jp112sdl/SplitFlap/Images/IMG_0931.jpeg

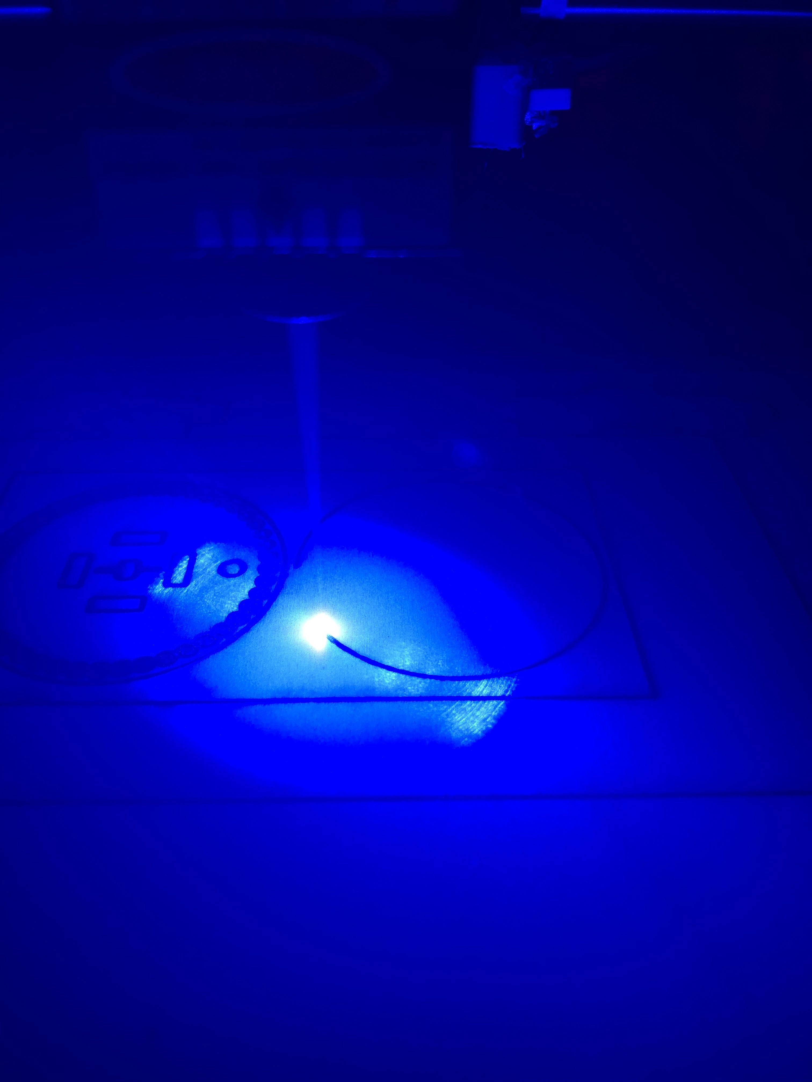
Images/IMG_0931.jpeg
