jp112sdl/SplitFlap/Images/IMG_0937.jpg

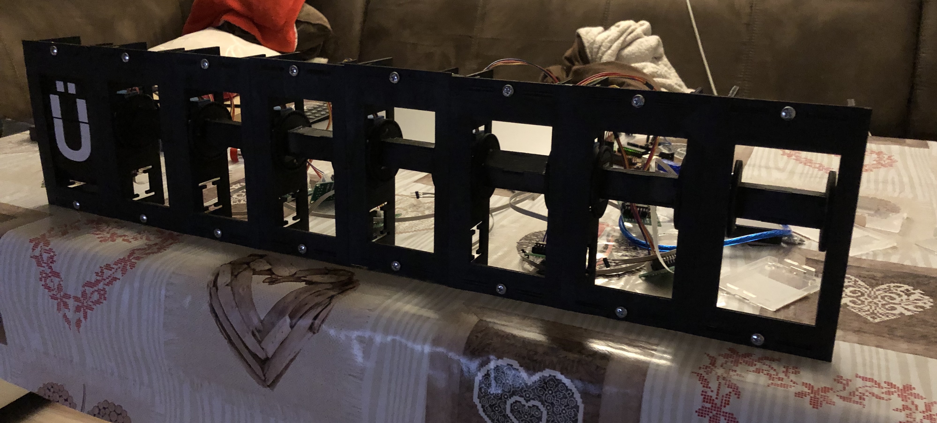
Images/IMG_0937.jpg
