jp112sdl/SplitFlap/Images/IMG_0946.jpeg

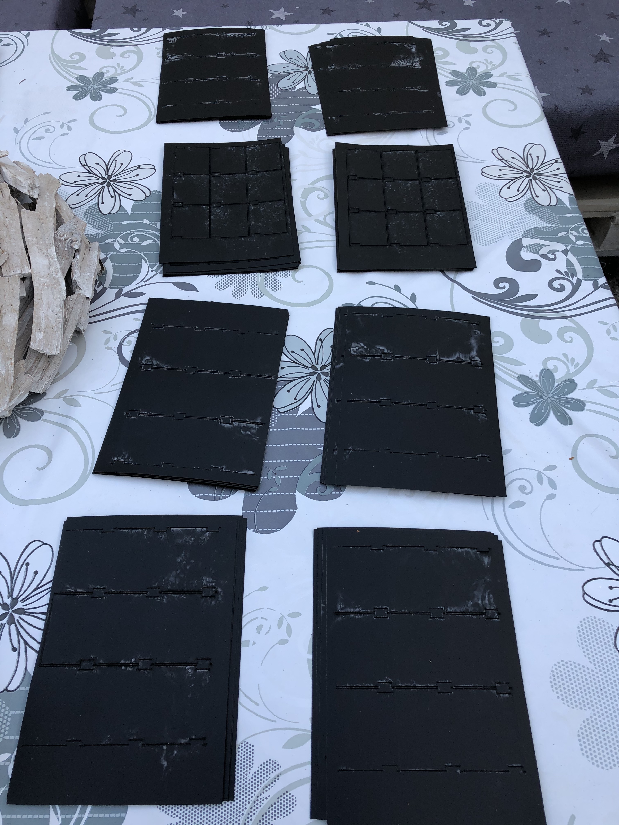
Images/IMG_0946.jpeg
