jp112sdl/SplitFlap/Images/IMG_0947.jpeg

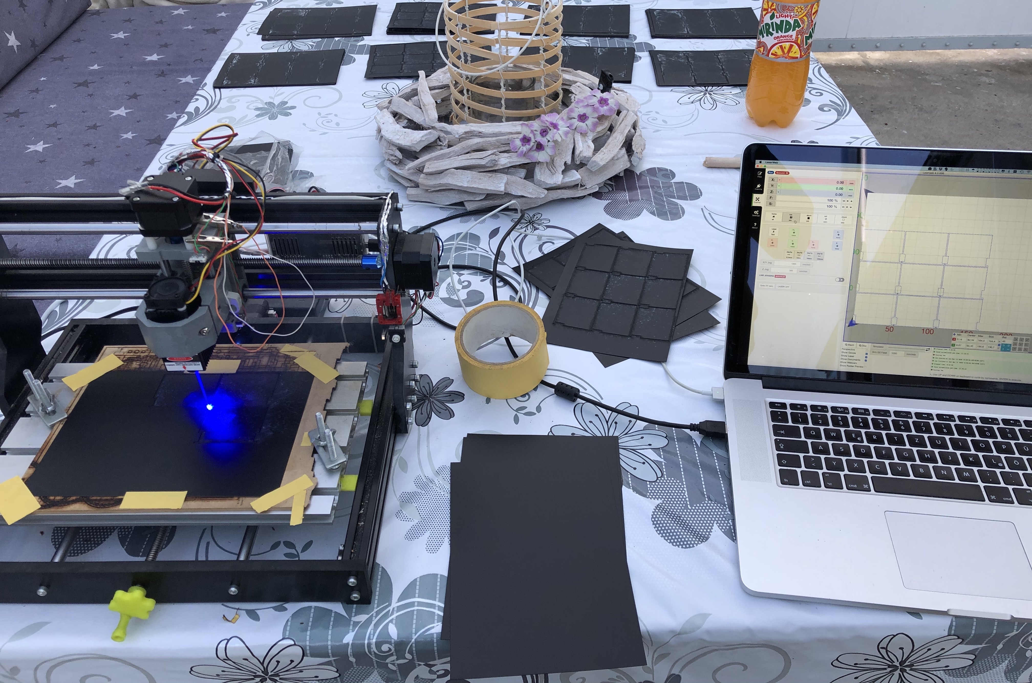
Images/IMG_0947.jpeg
