jp112sdl/SplitFlap/Images/IMG_0949.jpeg

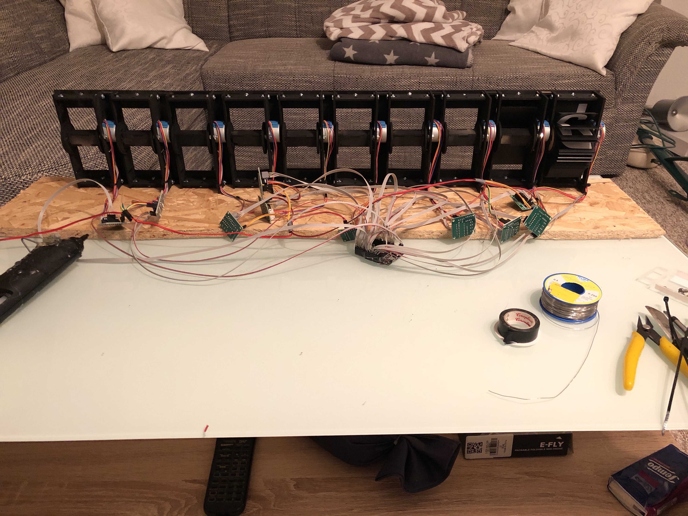
Images/IMG_0949.jpeg
