jp112sdl/SplitFlap/Images/IMG_0950.jpeg

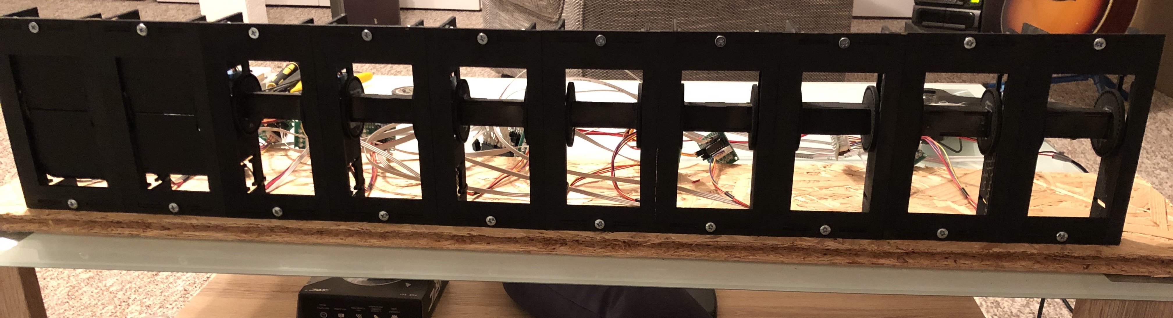
Images/IMG_0950.jpeg
