jp112sdl/SplitFlap/Images/IMG_0952.jpeg

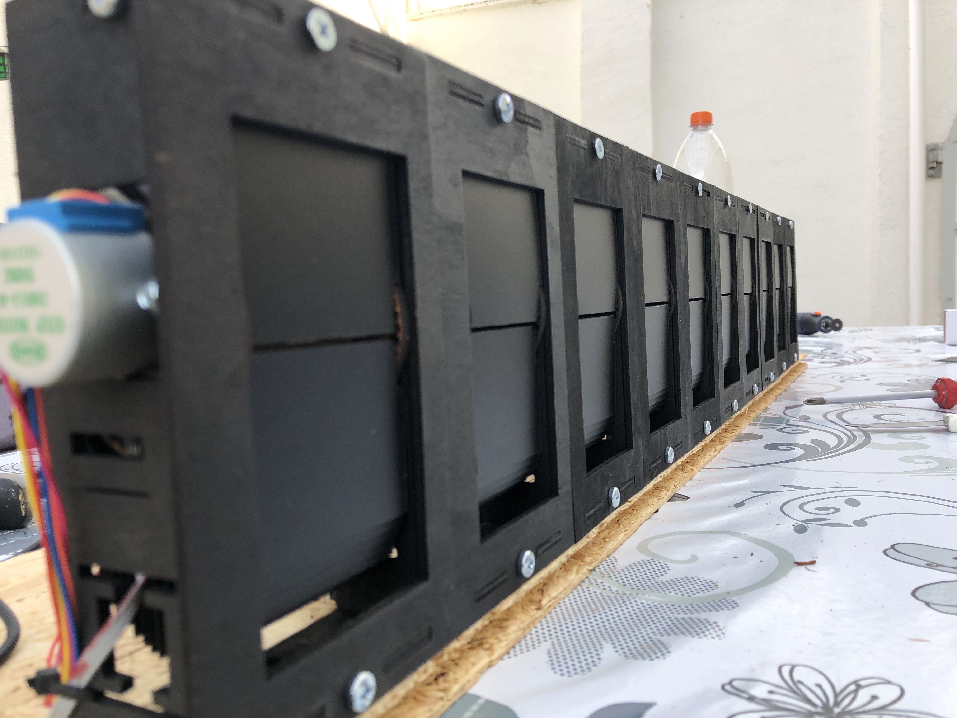
Images/IMG_0952.jpeg
