jp112sdl/SplitFlap/Images/IMG_0957.jpeg

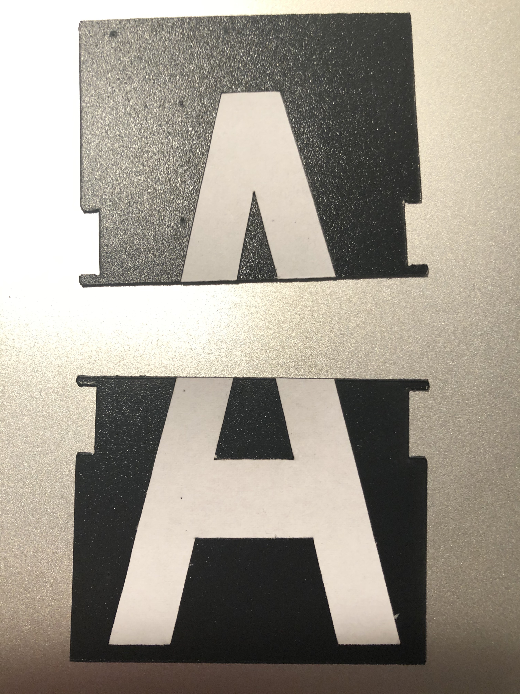
Images/IMG_0957.jpeg
