jp112sdl/SplitFlap/Images/IMG_0958.jpeg

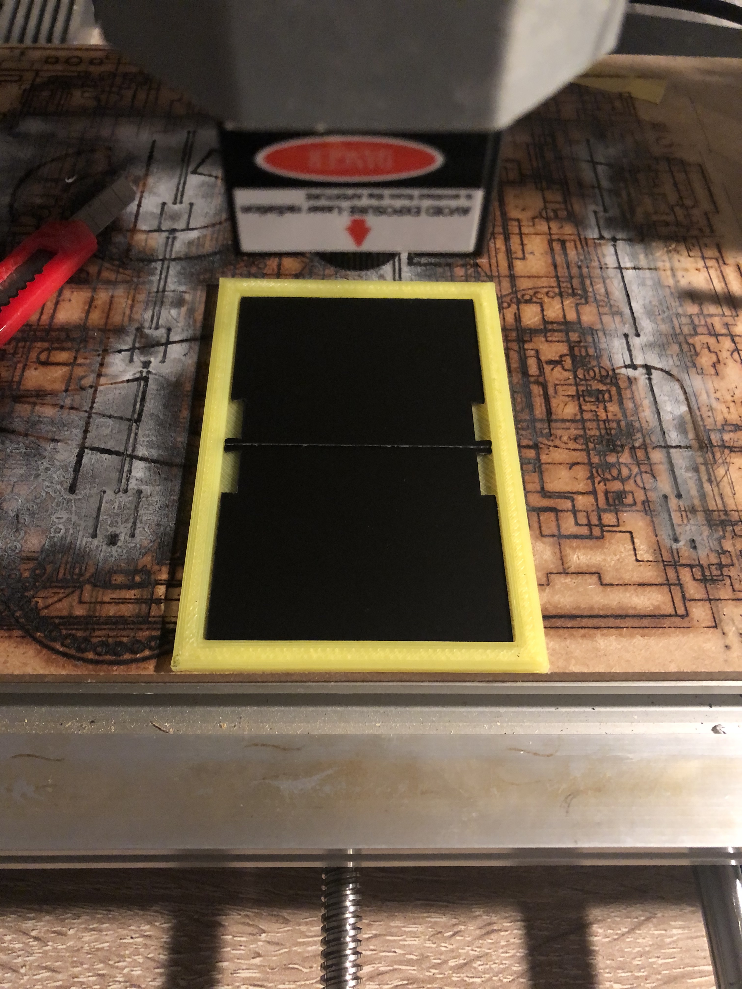
Images/IMG_0958.jpeg
