jp112sdl/SplitFlap/Images/IMG_0959.jpeg

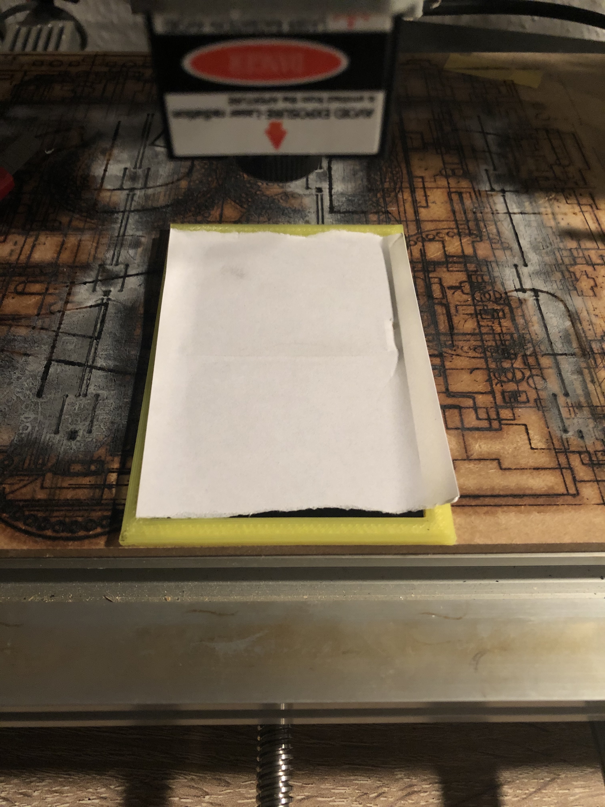
Images/IMG_0959.jpeg
