jp112sdl/SplitFlap/Images/IMG_0960.jpeg

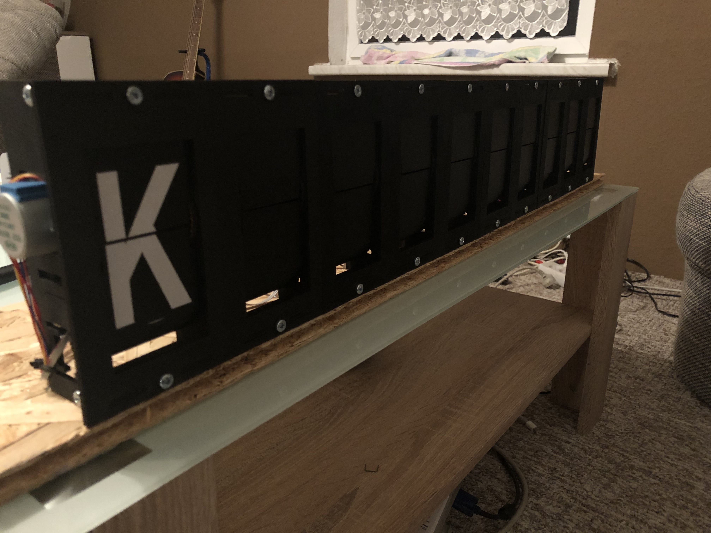
Images/IMG_0960.jpeg
