jp112sdl/SplitFlap/Images/IMG_0961.jpeg

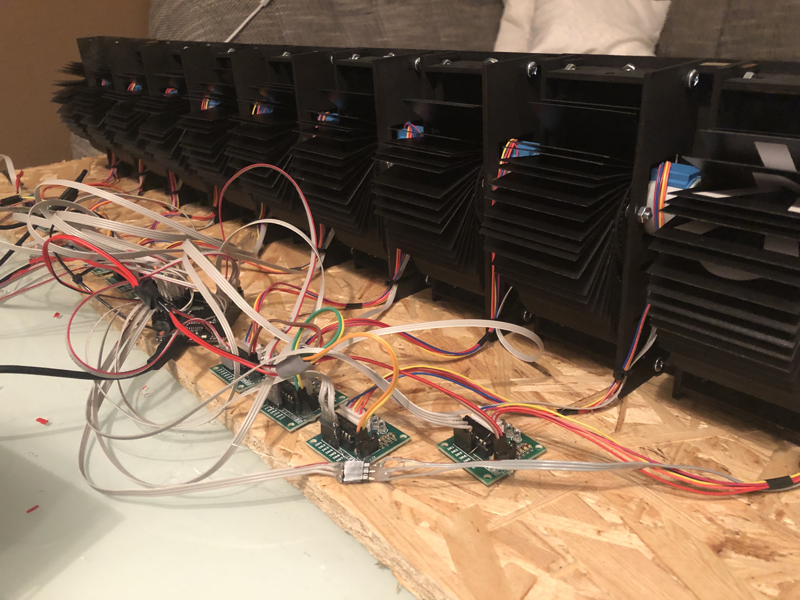
Images/IMG_0961.jpeg
