jp112sdl/SplitFlap/Images/IMG_0974.jpeg

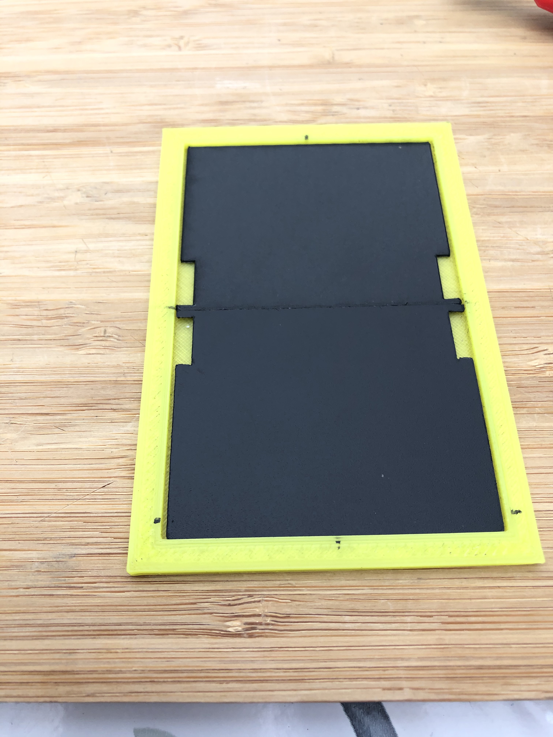
Images/IMG_0974.jpeg
