jp112sdl/SplitFlap/Images/IMG_0975.jpeg

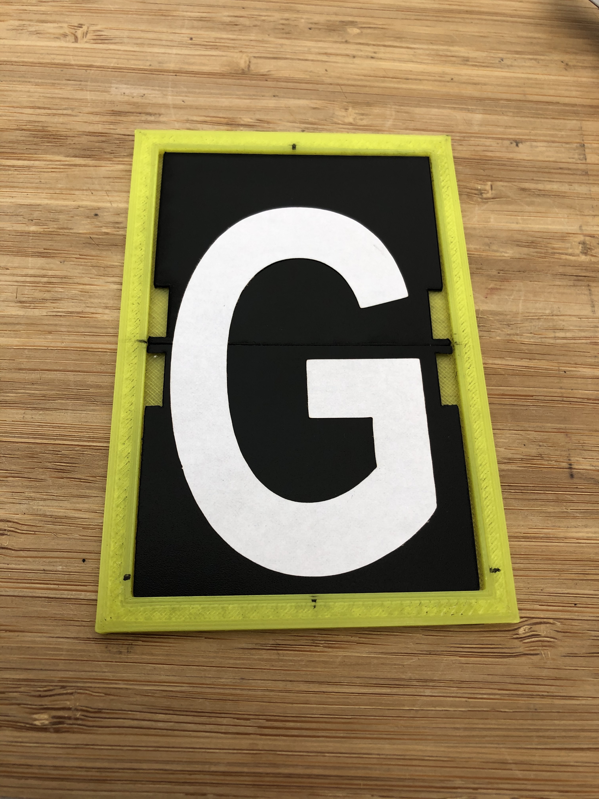
Images/IMG_0975.jpeg
