jp112sdl/SplitFlap/Images/IMG_0976.jpeg

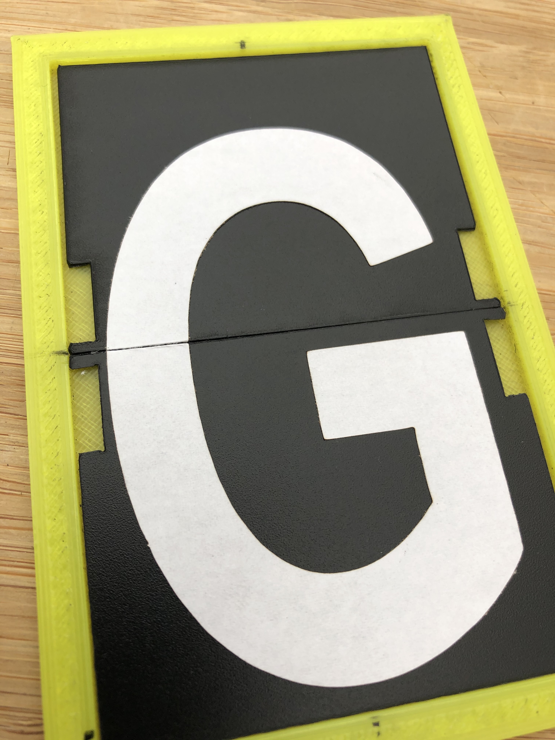
Images/IMG_0976.jpeg
