jp112sdl/SplitFlap/Images/IMG_0977.jpeg

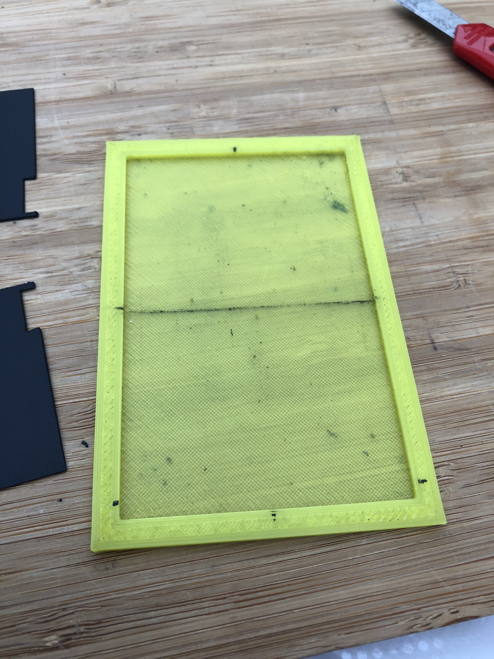
Images/IMG_0977.jpeg
