jp112sdl/SplitFlap/Images/IMG_0981.jpeg

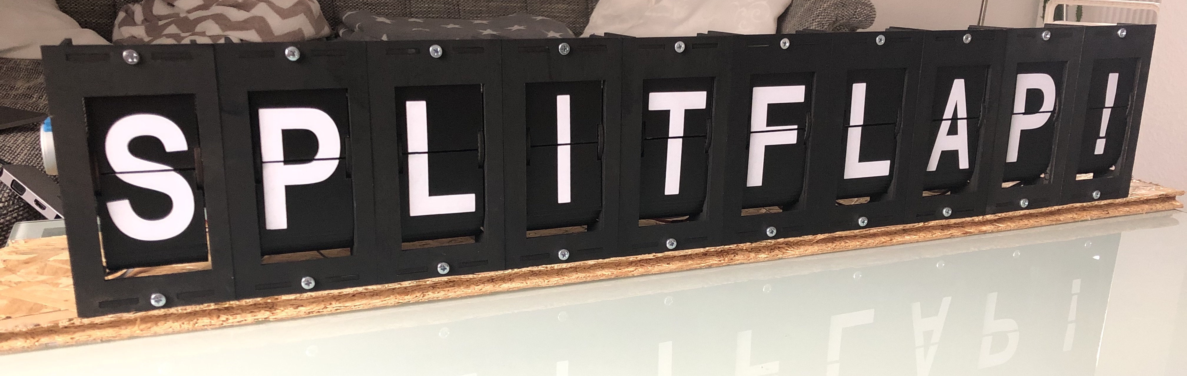
Images/IMG_0981.jpeg
