jp112sdl/SplitFlap/Images/IMG_0982.jpeg

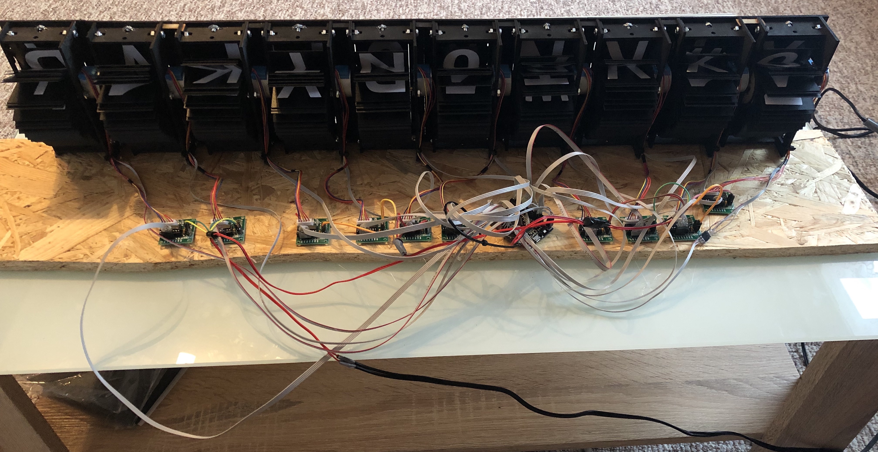
Images/IMG_0982.jpeg
