jp112sdl/SplitFlap/Images/IMG_1015.jpeg

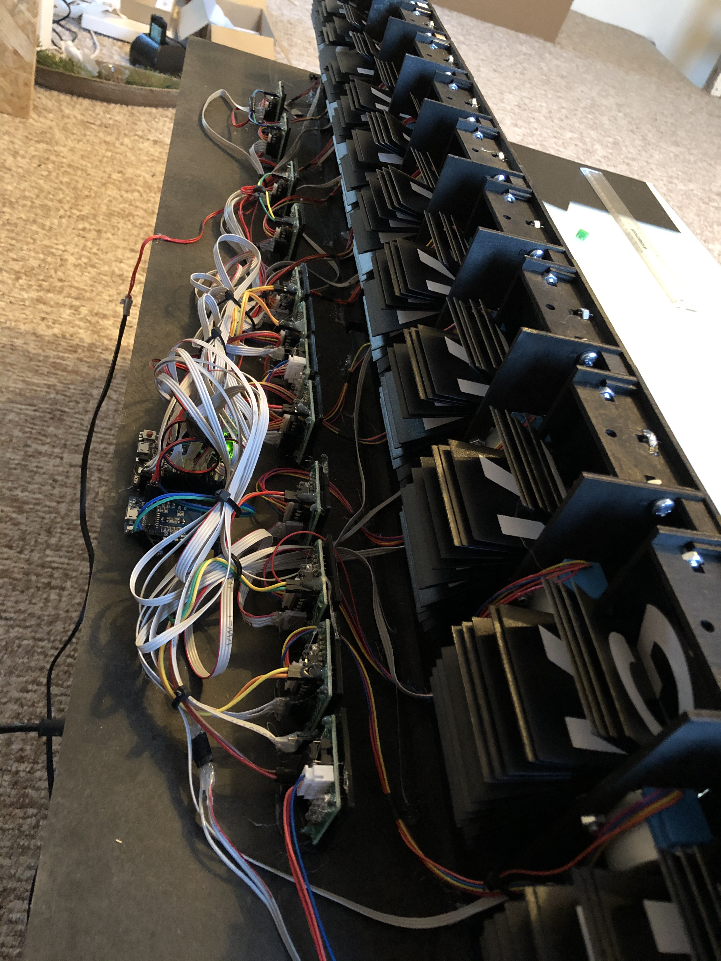
Images/IMG_1015.jpeg
