jp112sdl/SplitFlap/Images/IMG_1018.jpeg

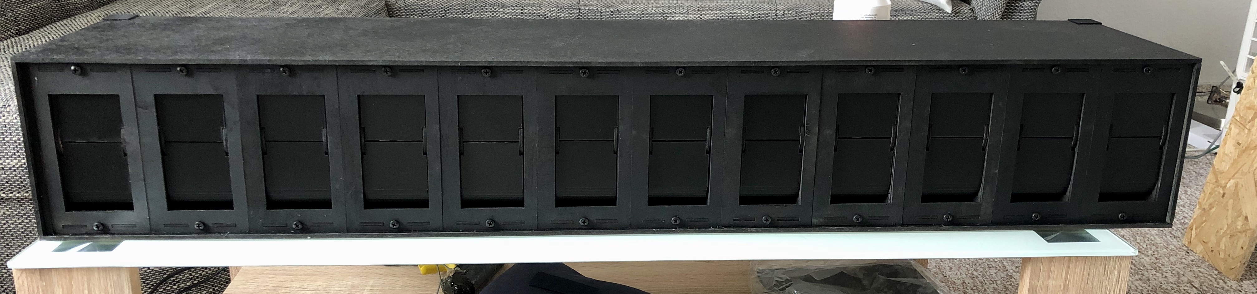
Images/IMG_1018.jpeg
