jp112sdl/SplitFlap/Images/IMG_1021.jpeg

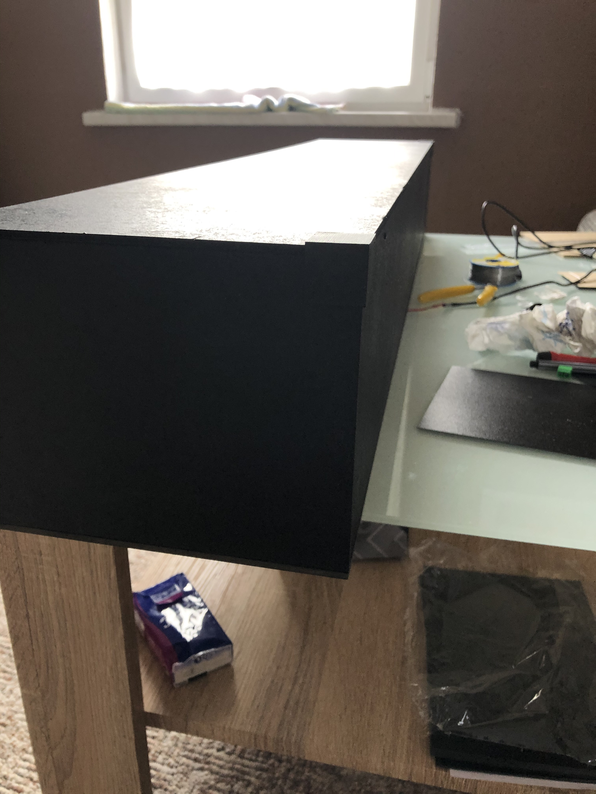
Images/IMG_1021.jpeg
