jp112sdl/SplitFlap/Images/IMG_1025.jpeg

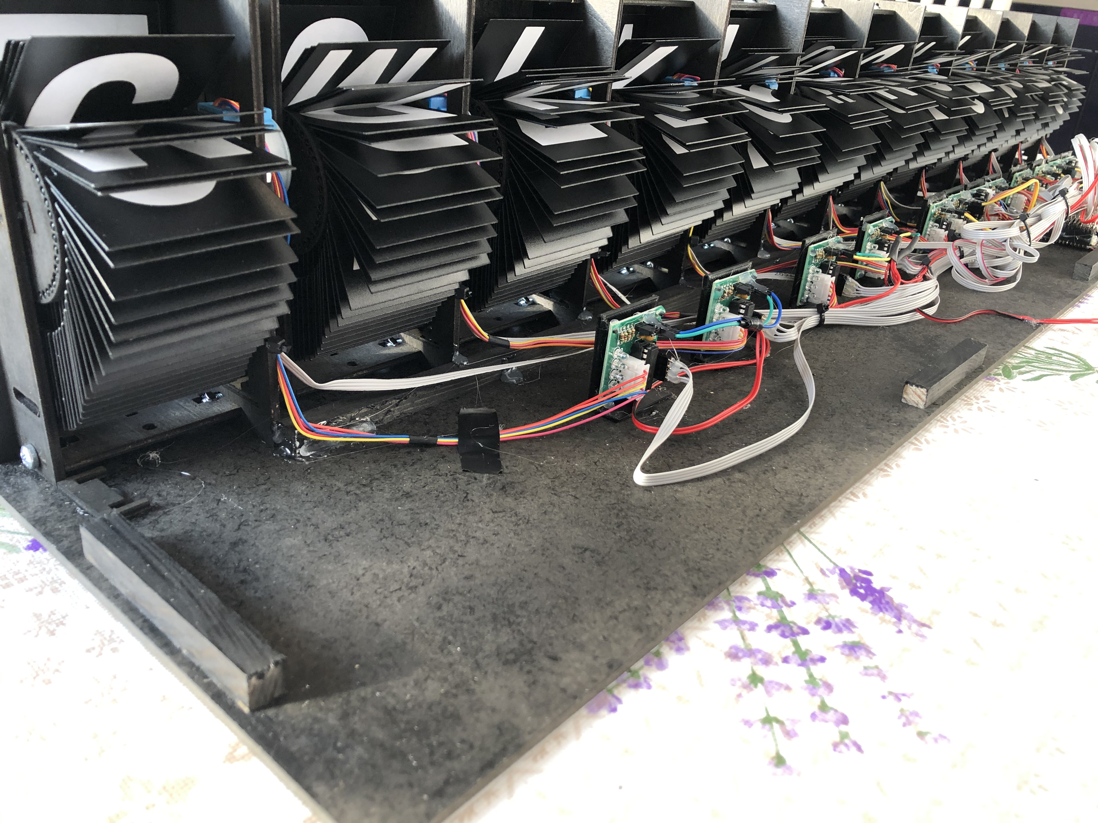
Images/IMG_1025.jpeg
