jp112sdl/SplitFlap/Images/IMG_2181.jpeg

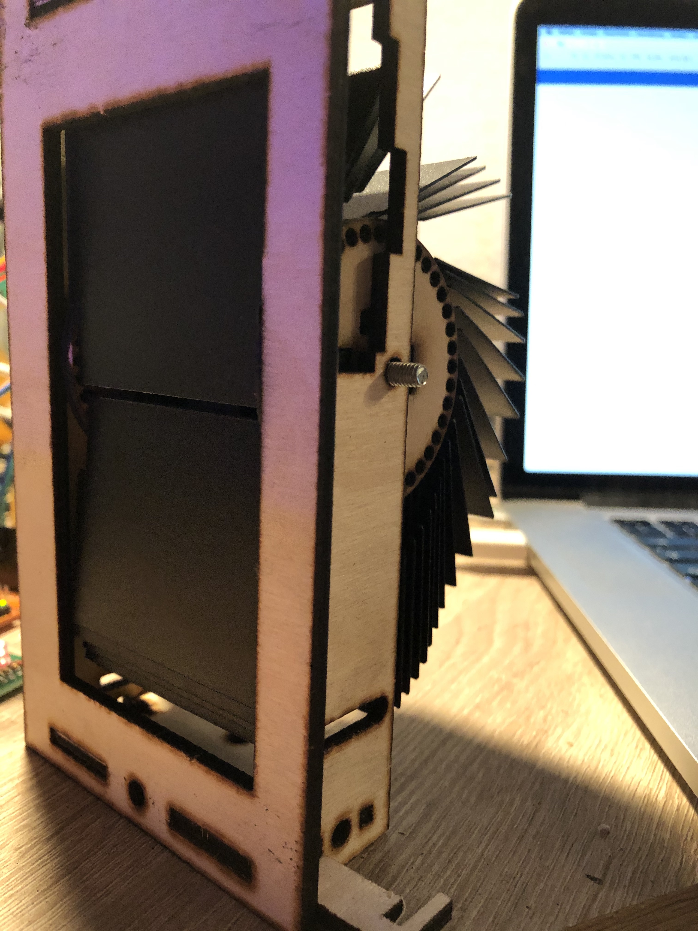
Images/IMG_2181.jpeg
