jp112sdl/SplitFlap/PCB/SplitFlap/SplitFlap.sch

## KiCad design PCB/SplitFlap/SplitFlap.sch (2020-03-11)

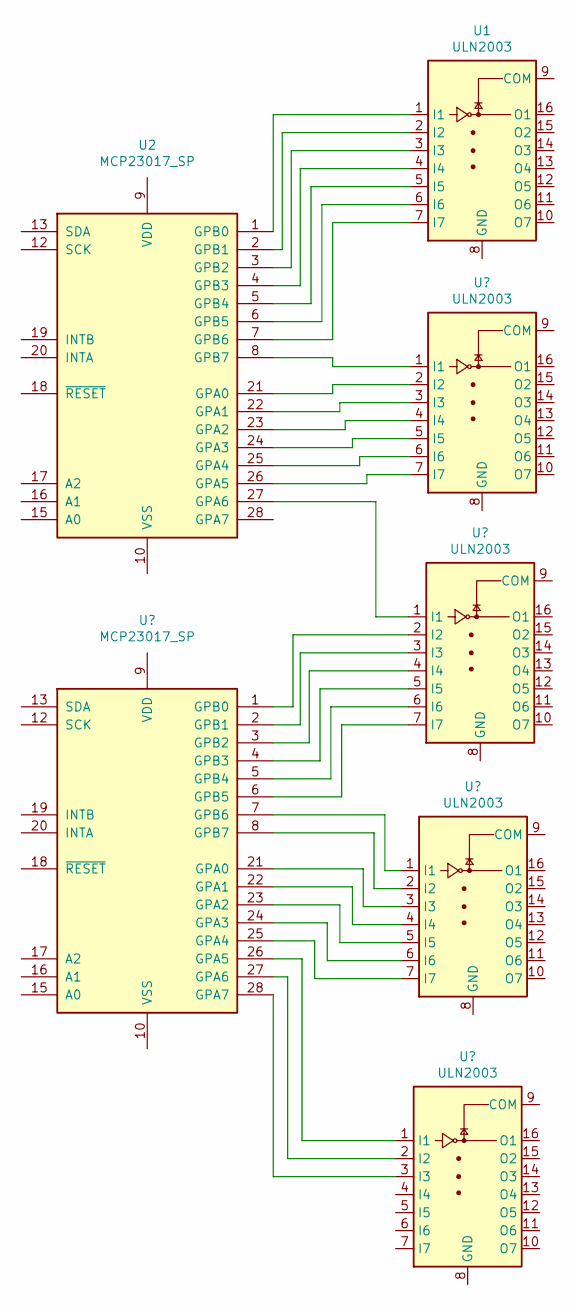
[picture p33: schematic SplitFlap.sch]

Parts:
U1: ULN2003; DIP-16_W7.62mm_LongPads
U2: MCP23017_SP; DIP-28_W7.62mm_LongPads

Connections:
unnamed: U1.1 (I1), U2.1 (GPB0)
unnamed: U1.2 (I2), U2.2 (GPB1)
unnamed: U1.3 (I3), U2.3 (GPB2)
unnamed: U1.4 (I4), U2.4 (GPB3)
unnamed: U1.5 (I5), U2.5 (GPB4)
unnamed: U1.6 (I6), U2.6 (GPB5)
unnamed: U1.7 (I7), U2.7 (GPB6)
